frankyhub/Wetterstation_TFT/png/3D.png

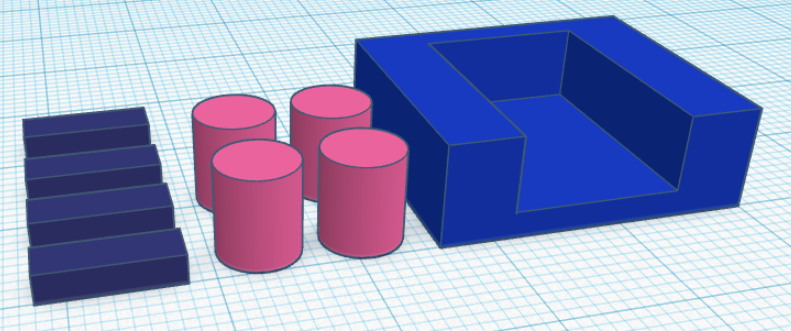
png/3D.png
