frankyhub/Wetterstation_TFT/png/10wetter.png

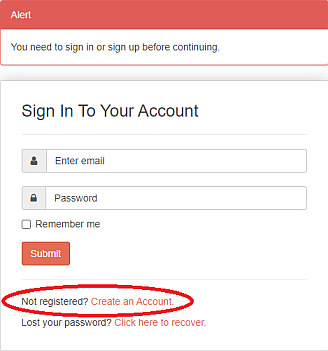
png/10wetter.png
