frankyhub/Wetterstation_TFT/png/datumuhrzeit.png

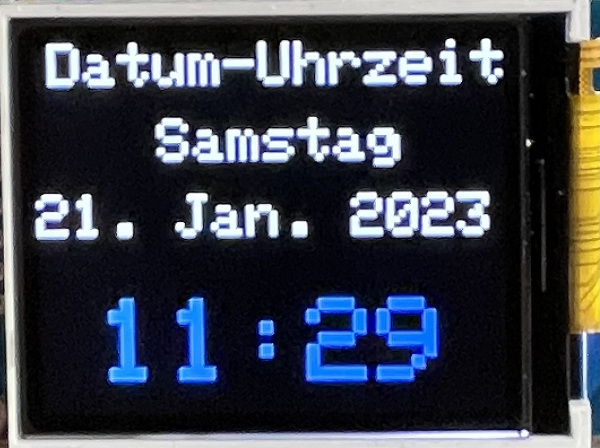
png/datumuhrzeit.png
