frankyhub/Wetterstation_TFT/png/DHT11_Verdrahtung.png

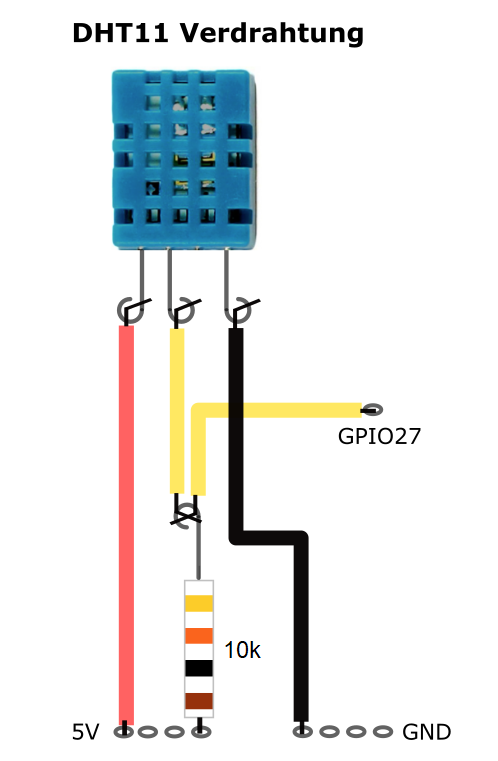
png/DHT11_Verdrahtung.png
