frankyhub/Wetterstation_TFT/png/espshield.png

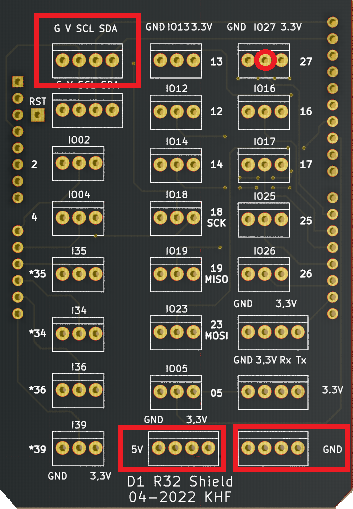
png/espshield.png
