frankyhub/Wetterstation_TFT/png/tft177_V.png

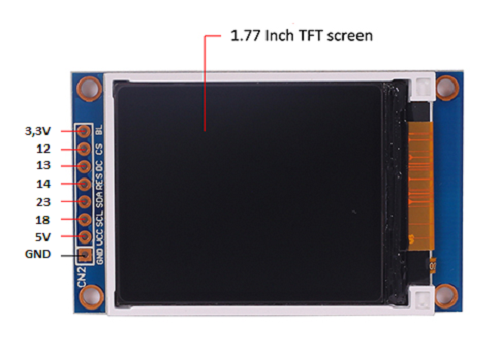
png/tft177_V.png
