frankyhub/Wetterstation_TFT/png/wetter5.JPG

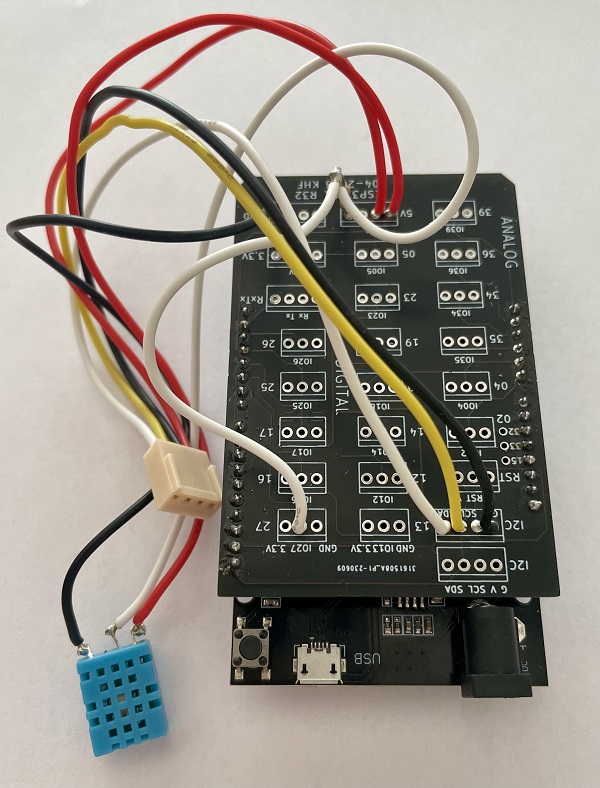
png/wetter5.JPG
